MedadRufus/MastersProject/Bike_logger/references/cyclical power.PNG

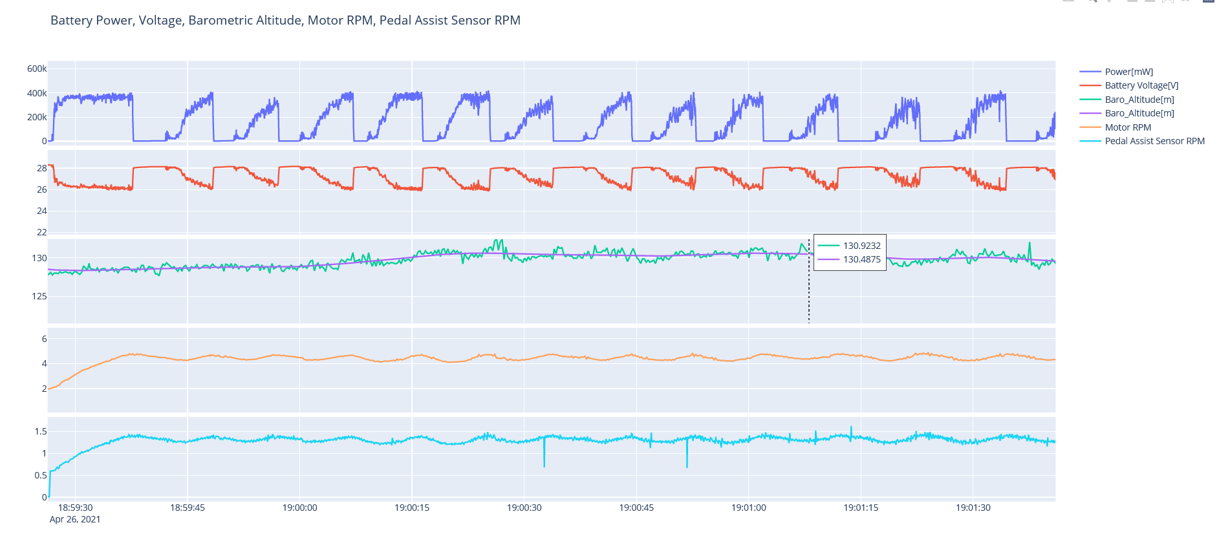
Bike_logger/references/cyclical power.PNG
