MedadRufus/MastersProject/Bike_logger/references/Discharge simulation.png

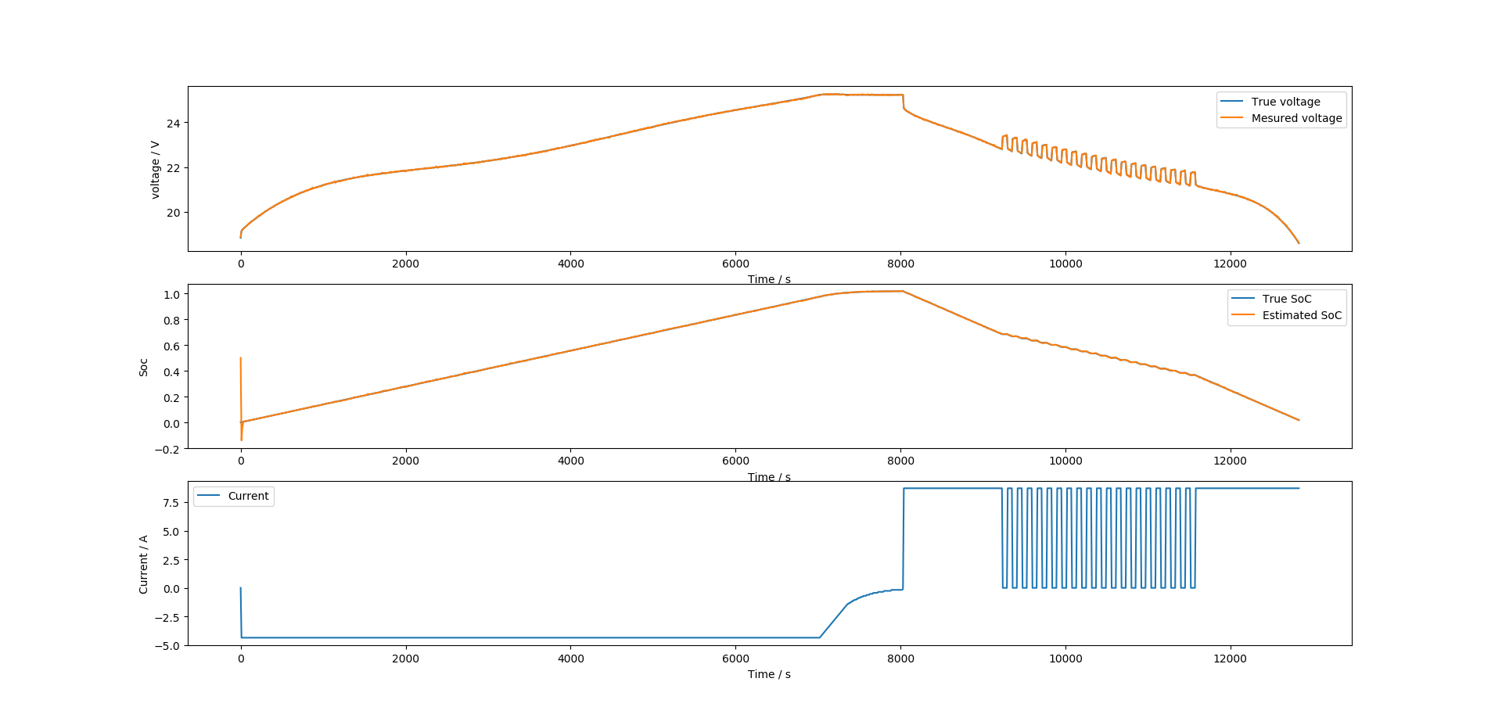
Bike_logger/references/Discharge simulation.png
