MedadRufus/MastersProject/Bike_logger/references/noise_on_brake_line.png

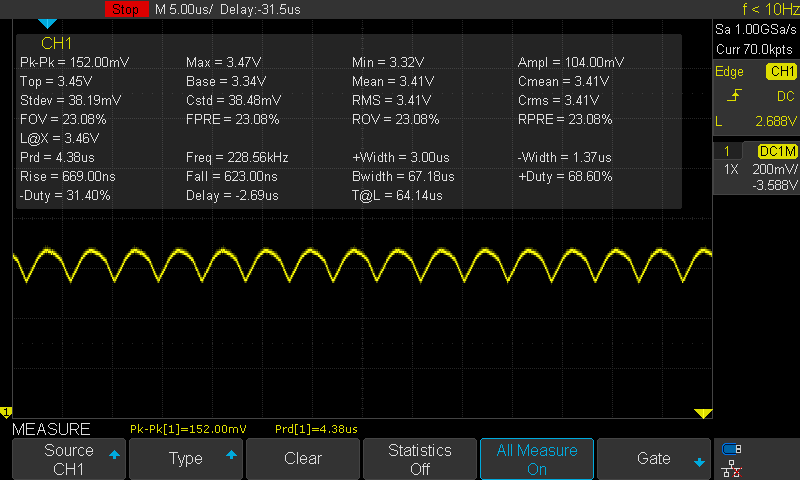
Bike_logger/references/noise_on_brake_line.png
