MedadRufus/MastersProject/Bike_logger/references/Plot prediction of power from slope.png

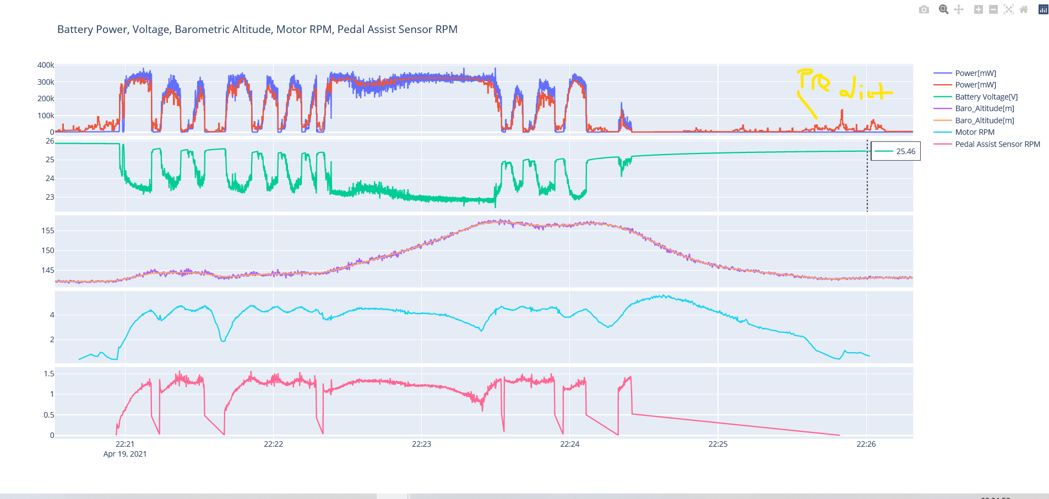
Bike_logger/references/Plot prediction of power from slope.png
