MedadRufus/MastersProject/Bike_logger/references/PNG/SDS00001.png

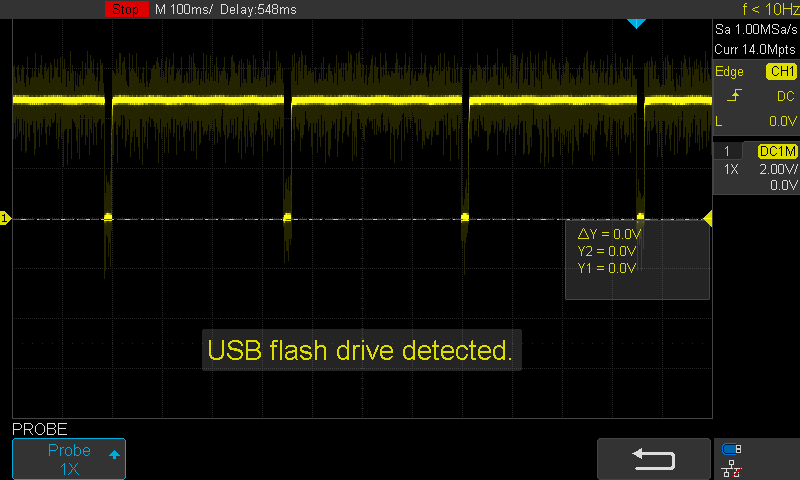
Bike_logger/references/PNG/SDS00001.png
