MedadRufus/MastersProject/Bike_logger/references/PNG/SDS00002.png

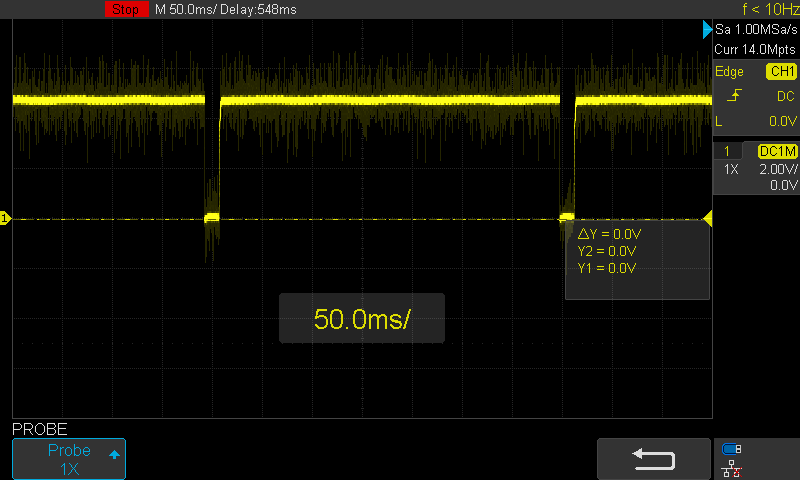
Bike_logger/references/PNG/SDS00002.png
