MedadRufus/MastersProject/Bike_logger/references/PNG/SDS00003.png

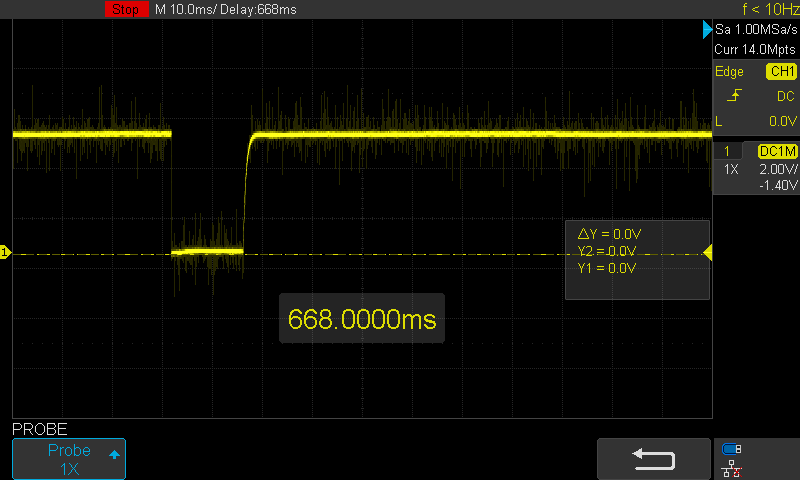
Bike_logger/references/PNG/SDS00003.png
