MedadRufus/MastersProject/Bike_logger/references/PNG/SDS00004.png

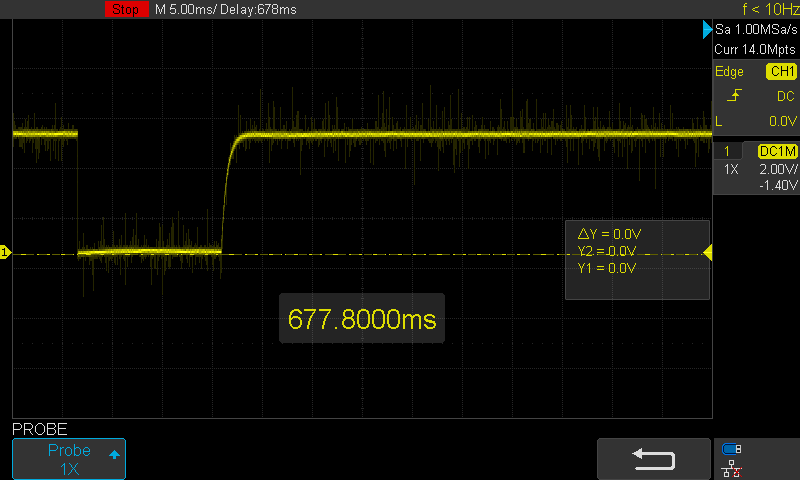
Bike_logger/references/PNG/SDS00004.png
