MedadRufus/MastersProject/Bike_logger/references/PNG/SDS00005.png

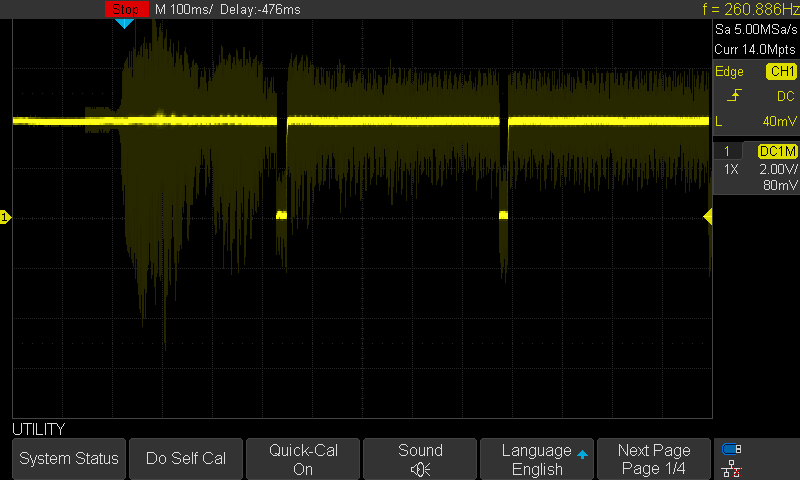
Bike_logger/references/PNG/SDS00005.png
