MedadRufus/MastersProject/Bike_logger/references/PNG/SDS00006.png

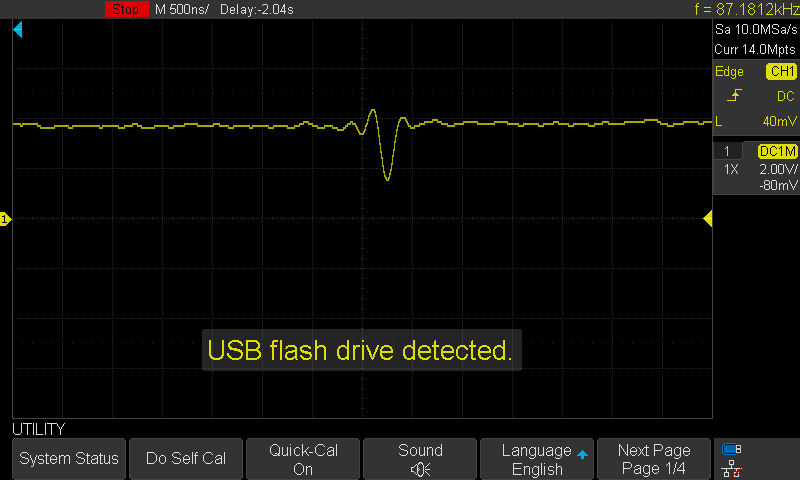
Bike_logger/references/PNG/SDS00006.png
