MedadRufus/MastersProject/Bike_logger/references/PNG/SDS00007.png

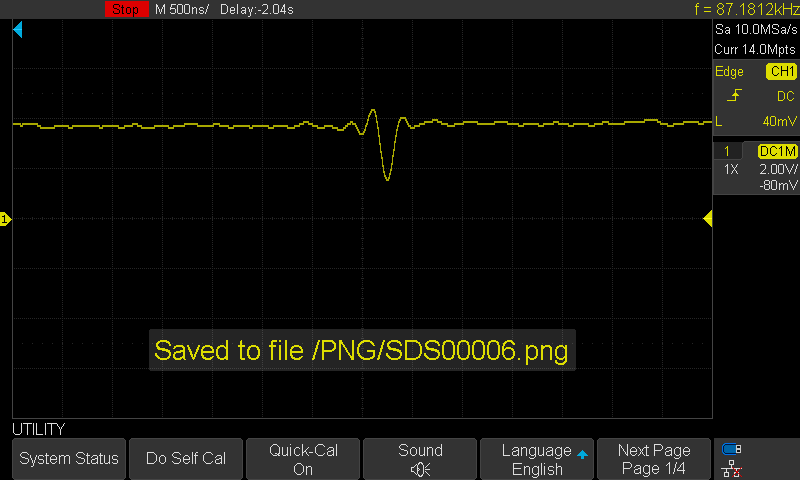
Bike_logger/references/PNG/SDS00007.png
