MedadRufus/MastersProject/Bike_logger/references/PNG/SDS00009.png

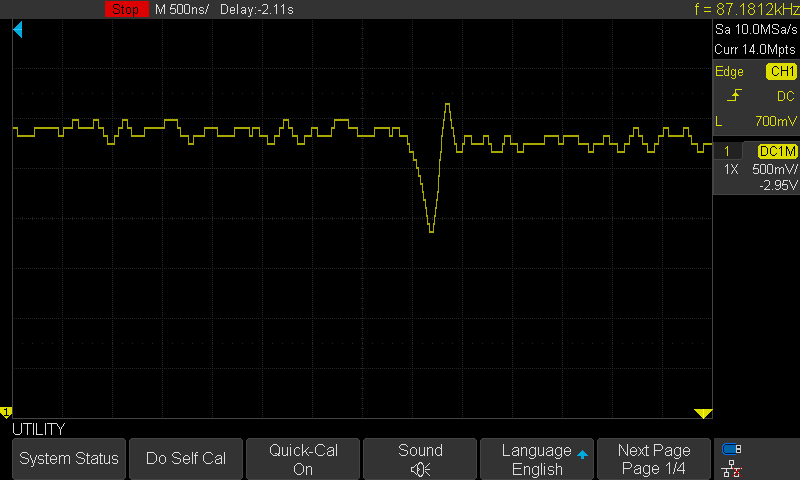
Bike_logger/references/PNG/SDS00009.png
