MedadRufus/MastersProject/Bike_logger/references/PNG/SDS00010.png

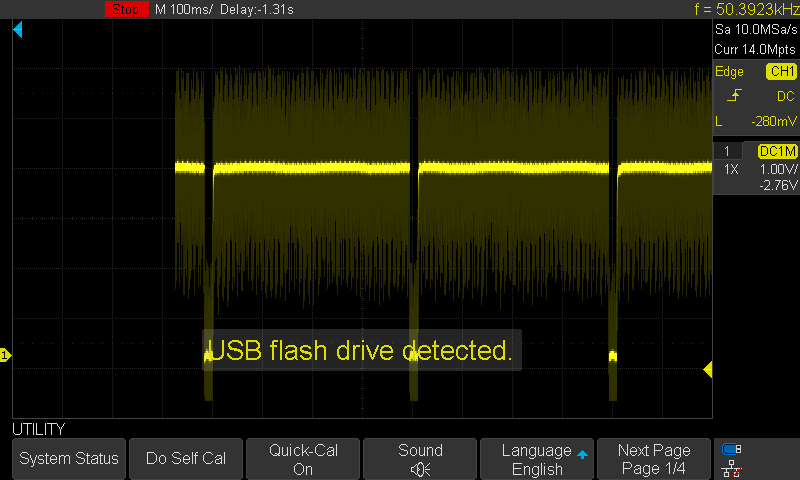
Bike_logger/references/PNG/SDS00010.png
