MedadRufus/MastersProject/Bike_logger/references/PNG/SDS00013.png

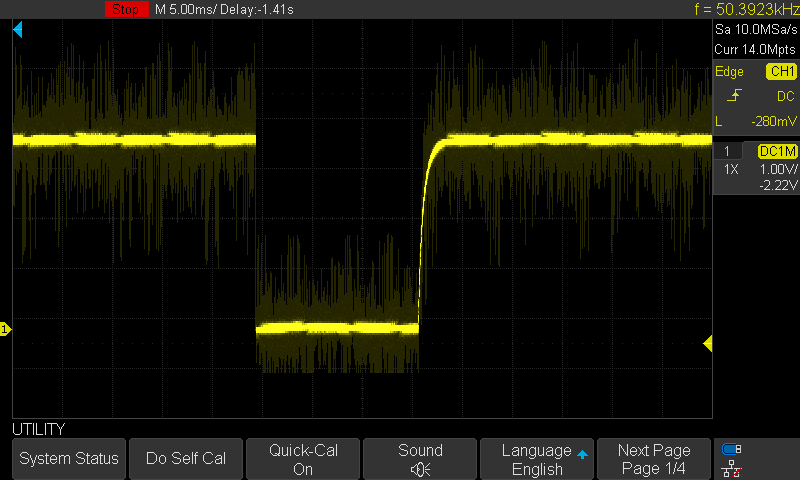
Bike_logger/references/PNG/SDS00013.png
