MedadRufus/MastersProject/Bike_logger/references/reference discharge plot.png

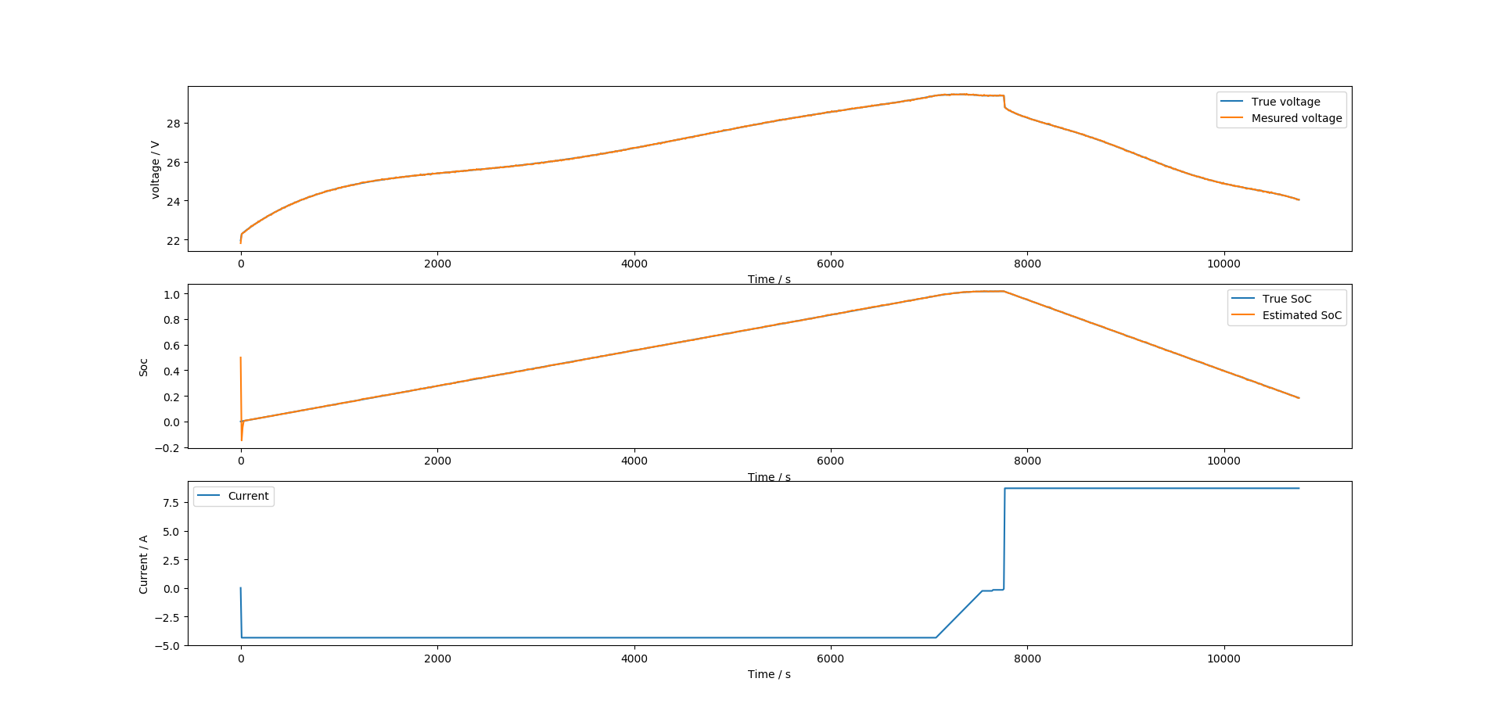
Bike_logger/references/reference discharge plot.png
