MedadRufus/MastersProject/Bike_logger/references/SDS00001.png

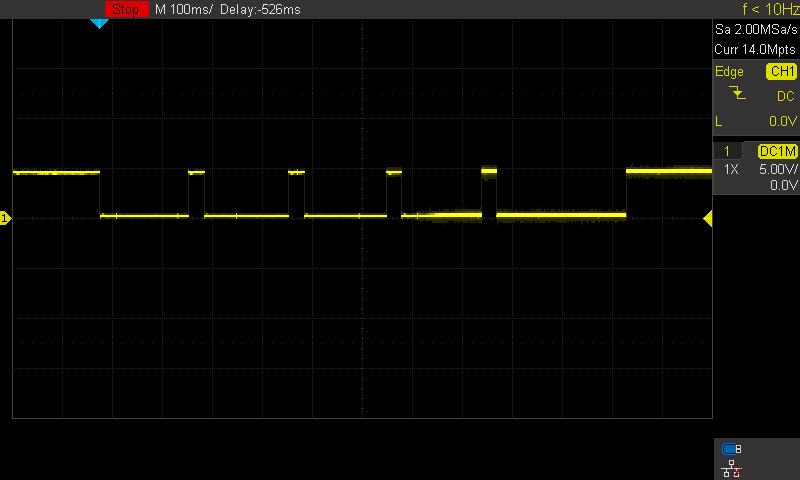
Bike_logger/references/SDS00001.png
