MedadRufus/MastersProject/Bike_logger/references/SDS00002.png

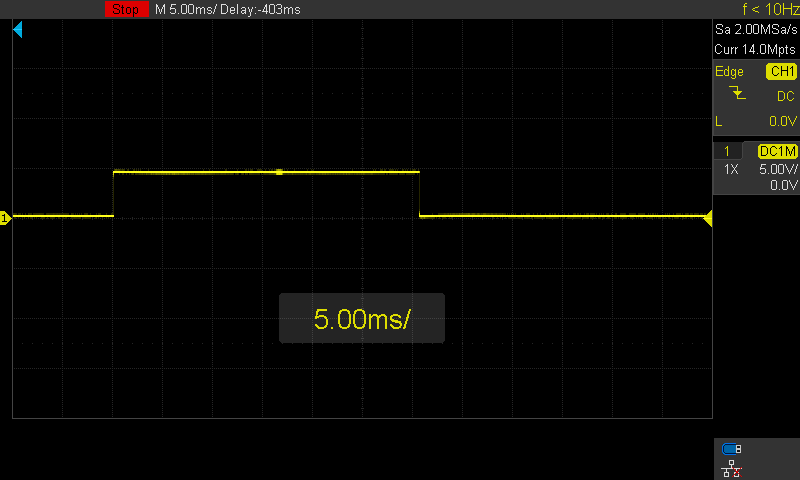
Bike_logger/references/SDS00002.png
