MedadRufus/MastersProject/Bike_logger/references/SDS00003.png

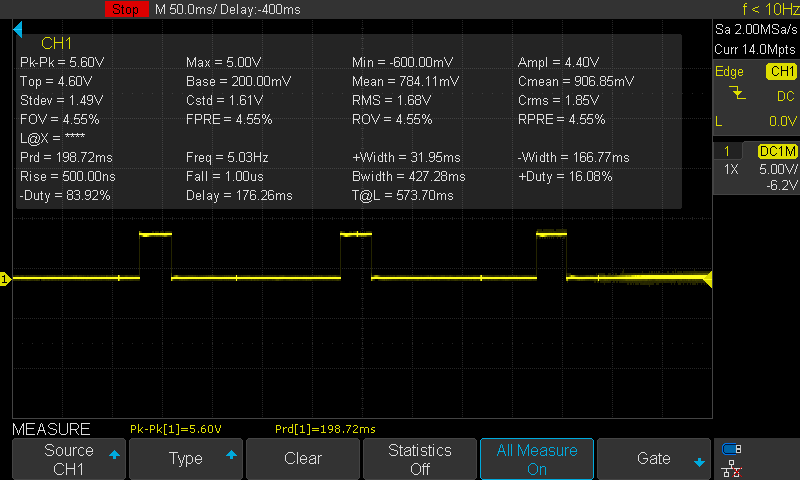
Bike_logger/references/SDS00003.png
