MedadRufus/MastersProject/Bike_logger/references/Low pass butterworth 4th order 10khz cutoff 10khz sample rate.png

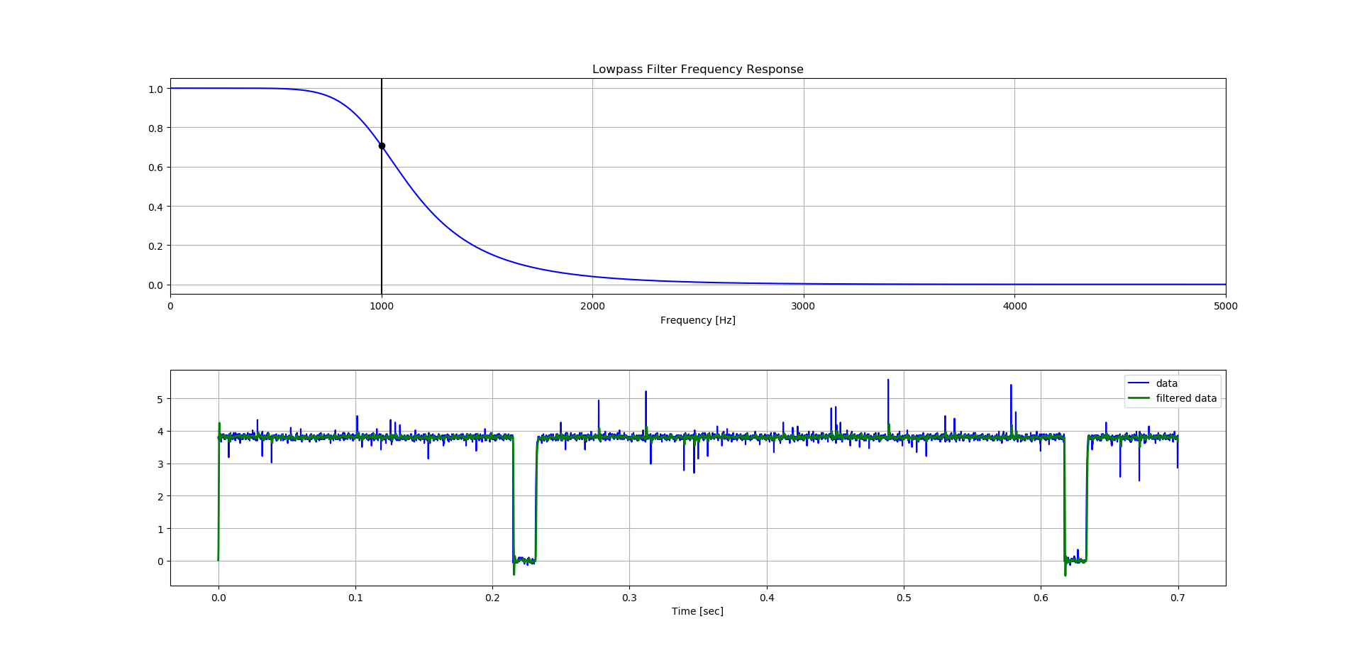
Bike_logger/references/Low pass butterworth 4th order 10khz cutoff 10khz sample rate.png
