MedadRufus/MastersProject/Bike_logger/references/Low pass butterworth 4th order 10000 cutoff.png

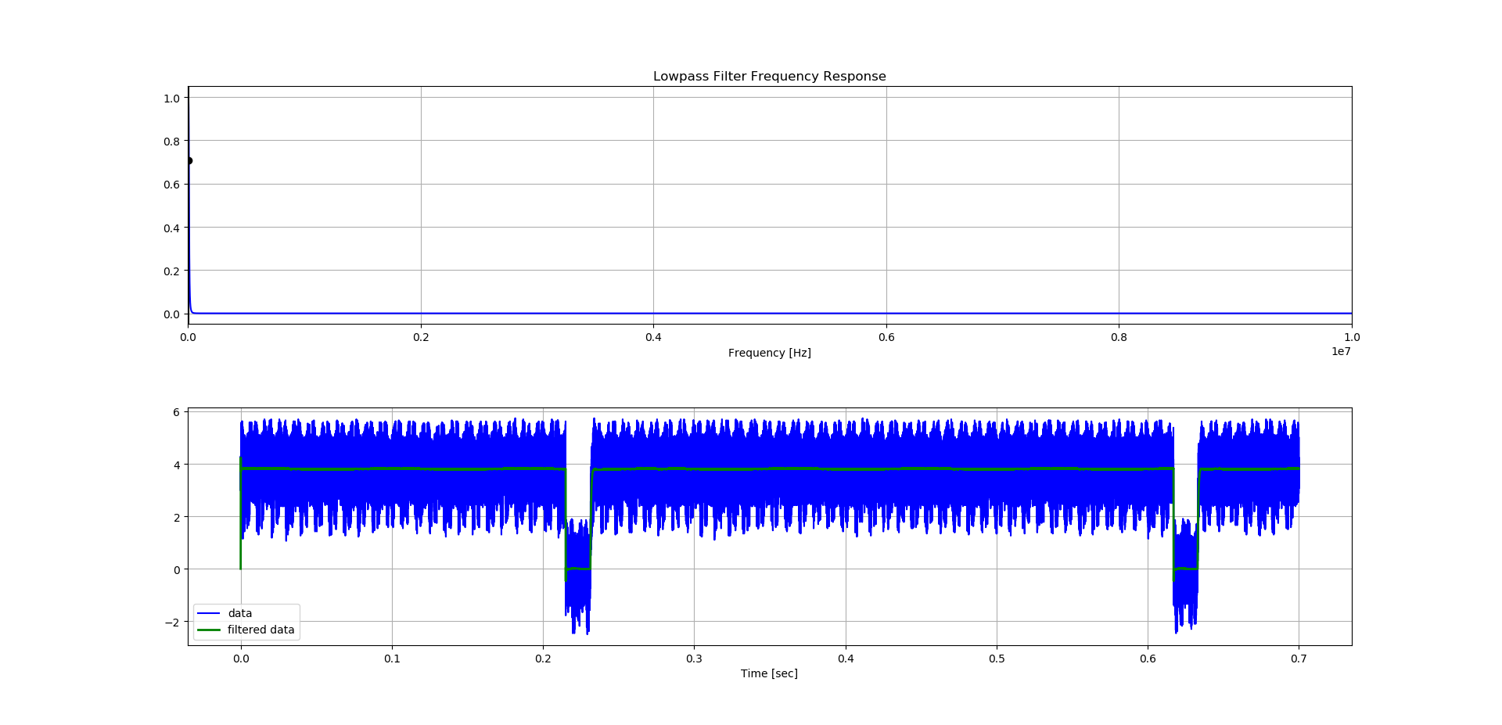
Bike_logger/references/Low pass butterworth 4th order 10000 cutoff.png
