MedadRufus/MastersProject/Bike_logger/references/Motor wiring.png

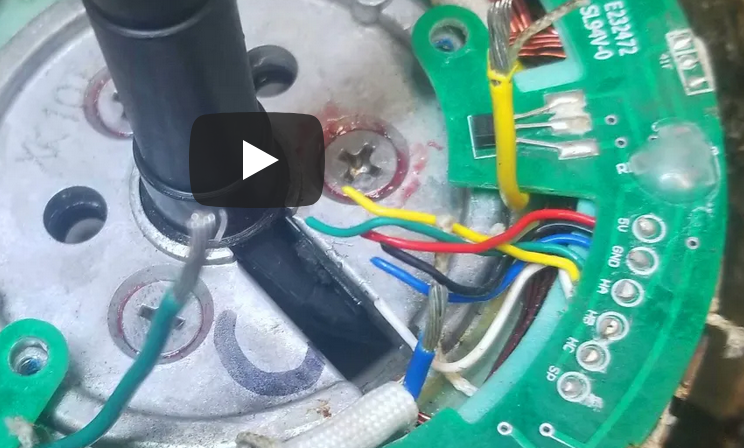
Bike_logger/references/Motor wiring.png
