MedadRufus/MastersProject/Bike_logger/Firmware/RTOS_sampling/src/state_logger/state_logger.hpp

/**
 * @file pulse_counter_adc.hpp
 * @author Medad Rufus Newman (mailto@medadnewman.co.uk)
 * @brief 
 * @version 0.1
 * @date 2021-04-19
 * 
 * @copyright Copyright (c) 2021
 * 
 */

void init_state_logger();
