MedadRufus/MastersProject/Bike_logger/Firmware/Firmware/Firmware.ino

/*********************************************************************
** @source Ebike Blackbox datalogger
**
** Main code for the Ebike logger
**
** @author Copyright (C) 2021  Medad Rufus Newman
** @version v0.1
********************************************************************/


/* ==================================================================== */
/* ========================== include files =========================== */
/* ==================================================================== */


/* Inclusion of system and local header files goes here */
#include <StateMachine.h>
#include "SparkFunLSM6DS3.h"
#include "Wire.h"
#include "SPI.h"
#include "ms8607.h"
#include "sd_card_manager.h"
#include <SparkFun_u-blox_GNSS_Arduino_Library.h> //http://librarymanager/All#SparkFun_u-blox_GNSS



/* ==================================================================== */
/* ============================ constants ============================= */
/* ==================================================================== */

/* #define and enum statements go here */

#define LED_PIN 27

#define RXD2 17
#define TXD2 16

/* ==================================================================== */
/* ======================== global variables ========================== */
/* ==================================================================== */

/* Global variables definitions go here */

StateMachine blinker1(100, true);
StateMachine poll_imu(1000, true);
StateMachine poll_baro(100, true);
StateMachine poll_gps(500, true);
StateMachine poll_IN226(10, true);
StateMachine write_to_sd(10, true);

const int led1 = LED_PIN;
bool state1 = false;   // false is OFF, true is ON

static ms8607 m_ms8607;
LSM6DS3 myIMU; //Default constructor is I2C, addr 0x6B
SD_Manager sd_manager;
SFE_UBLOX_GNSS myGNSS;

struct SensorData
{
  public:
    /* GPS related */
    uint32_t longitude;
    uint32_t latitude;
    uint32_t altitude;
    uint32_t velocity;
    uint32_t sats;

    /* Acceleration/Gyroscope */
    float acc_x;
    float acc_y;
    float acc_z;
    float gyro_x;
    float gyro_y;
    float gyro_z;
    float imu_temperature;

    /* Current voltage */
    int32_t current_discharge;
    int32_t voltage_discharge;
    int32_t current_charge;
    int32_t voltage_charge;

    /* Temperature/pressure/humidity */
    float temperature;
    float pressure;
    float humidity;

    /* Other physical inputs */
    int32_t pedal_rpm;
    bool brake_state;
    int32_t motor_speed;
};

SensorData sensor_data;

char buffer1 [50];
char buffer2 [200];
char buffer_gnss [400];


/* ==================================================================== */
/* ============================== data ================================ */
/* ==================================================================== */

/* Definition of datatypes go here */



/* ==================================================================== */
/* ==================== function prototypes =========================== */
/* ==================================================================== */

/* Function prototypes for public (external) functions go here */


/* ==================================================================== */
/* ============================ functions ============================= */
/* ==================================================================== */

void setup()
{
  pinMode(led1, OUTPUT);
  digitalWrite(led1, state1 ? HIGH : LOW);
  Wire.begin(21, 22); // Acclerometer/gyro/temperature/pressure/humidity sensor
  Wire.setClock(400000);

  Serial.begin(2000000);
  Serial.println("=======================================================");
  Serial.println("================ Ebike BlackBox =======================");
  Serial.println("============== By Medad Rufus Newman ==================");
  Serial.println("======= with assistance from Richard Ibbotson =========");
  Serial.println("=======================================================");

  /* Initialise the IMU */
  init_imu();


  m_ms8607.begin();
  if (m_ms8607.is_connected() == true) {
    m_ms8607.reset();
  }

  boolean connected = m_ms8607.is_connected();
  Serial.println(connected ? "MS8607 Sensor connencted" : "MS8607 Sensor disconnected");

  /* initiliase the SD card manager */
  sd_manager.SD_Manager_init();


  /* Setup GNSS */
  Serial1.begin(9600, SERIAL_8N1, RXD2, TXD2);
  //myGNSS.enableDebugging(); // Uncomment this line to enable helpful debug messages on Serial
  if (myGNSS.begin(Serial1) == false) //Connect to the u-blox module using Wire port
  {
    Serial.println(F("u-blox GNSS not detected"));
  }
  myGNSS.setI2COutput(COM_TYPE_UBX); //Set the I2C port to output UBX only (turn off NMEA noise)
  myGNSS.setNavigationFrequency(2); //Produce two solutions per second
  myGNSS.setAutoPVTcallback(&logPVTdata); // Enable automatic NAV PVT messages with callback to printPVTdata

}


void loop()
{
  if (blinker1.update()) {
    state1 = !state1;
    digitalWrite(led1, state1 ? HIGH : LOW);
  }

  if (poll_imu.update()) {
    //update_imu_data();
  }

  if (poll_baro.update()) {
    update_baro_data();
  }

  if (poll_gps.update()) {
    update_gnss_data();
  }

  if (poll_IN226.update()) {
  }

  if (write_to_sd.update()) {
  }
}

/* Update GNSS data */
void update_gnss_data()
{
  myGNSS.checkUblox(); // Check for the arrival of new data and process it.
  myGNSS.checkCallbacks(); // Check if any callbacks are waiting to be processed.
}

/* Update the sensor data struct with baro values

*/
void update_baro_data()
{
  //Get all parameters
  m_ms8607.read_temperature_pressure_humidity(&sensor_data.temperature, &sensor_data.pressure,
      &sensor_data.humidity);


  /* Write baro data to file */
  sprintf (buffer1, "%f,%f,%f\n", sensor_data.temperature, sensor_data.pressure, sensor_data.humidity);
  Serial.print(buffer1);
  sd_manager.appendFileSimple("/baro.csv", buffer1);

}


void init_imu()
{

  //Over-ride default settings if desired
  myIMU.settings.gyroEnabled = 1;  //Can be 0 or 1
  myIMU.settings.gyroRange = 2000;   //Max deg/s.  Can be: 125, 245, 500, 1000, 2000
  myIMU.settings.gyroSampleRate = 833;   //Hz.  Can be: 13, 26, 52, 104, 208, 416, 833, 1666
  myIMU.settings.gyroBandWidth = 200;  //Hz.  Can be: 50, 100, 200, 400;
  myIMU.settings.gyroFifoEnabled = 1;  //Set to include gyro in FIFO
  myIMU.settings.gyroFifoDecimation = 1;  //set 1 for on /1

  myIMU.settings.accelEnabled = 1;
  myIMU.settings.accelRange = 16;      //Max G force readable.  Can be: 2, 4, 8, 16
  myIMU.settings.accelSampleRate = 833;  //Hz.  Can be: 13, 26, 52, 104, 208, 416, 833, 1666, 3332, 6664, 13330
  myIMU.settings.accelBandWidth = 200;  //Hz.  Can be: 50, 100, 200, 400;
  myIMU.settings.accelFifoEnabled = 1;  //Set to include accelerometer in the FIFO
  myIMU.settings.accelFifoDecimation = 1;  //set 1 for on /1
  myIMU.settings.tempEnabled = 1;

  //Non-basic mode settings
  myIMU.settings.commMode = 1;

  //FIFO control settings
  myIMU.settings.fifoThreshold = 4095;  //Can be 0 to 4095 (16 bit bytes)
  myIMU.settings.fifoSampleRate = 100;  //Hz.  Can be: 10, 25, 50, 100, 200, 400, 800, 1600, 3300, 6600
  myIMU.settings.fifoModeWord = 6;  //FIFO mode.
  //FIFO mode.  Can be:
  //  0 (Bypass mode, FIFO off)
  //  1 (Stop when full)
  //  3 (Continuous during trigger)
  //  4 (Bypass until trigger)
  //  6 (Continous mode)

  //Call .begin() to configure the IMUs
  if ( myIMU.begin() != 0 )
  {
    Serial.println("Problem starting the IMU sensor");
  }
  else
  {
    Serial.println("Sensor IMU started.");
  }

  Serial.print("Configuring FIFO with no error checking...");
  myIMU.fifoBegin();
  Serial.print("Done!\n");

  Serial.print("Clearing out the FIFO...");
  myIMU.fifoClear();
  Serial.print("Done!\n");
}


/* Update the sensor data struct with imu values

*/
void update_imu_data()
{
  float temp;  //This is to hold read data

  //Now loop until FIFO is empty.  NOTE:  As the FIFO is only 8 bits wide,
  //the channels must be synchronized to a known position for the data to align
  //properly.  Emptying the fifo is one way of doing this (this example)
  while ( ( myIMU.fifoGetStatus() & 0x1000 ) == 0 ) {


    sprintf (buffer2, "%f,%f,%f,%f,%f,%f\n",
             myIMU.calcGyro(myIMU.fifoRead()),
             myIMU.calcGyro(myIMU.fifoRead()),
             myIMU.calcGyro(myIMU.fifoRead()),
             myIMU.calcAccel(myIMU.fifoRead()),
             myIMU.calcAccel(myIMU.fifoRead()),
             myIMU.calcAccel(myIMU.fifoRead())
            );

    Serial.print(buffer2);
    sd_manager.appendFileSimple("/imu.csv", buffer2);


  }

}


/*  Callback: printPVTdata will be called when new NAV PVT data arrives
    See u-blox_structs.h for the full definition of UBX_NAV_PVT_data_t
*/
void logPVTdata(UBX_NAV_PVT_data_t ubxDataStruct)
{

  sprintf (buffer_gnss,"%02u,%02u,%02u,%03u,%d,%d,%d,%d,%d,%d,%d\n",
          ubxDataStruct.hour,
          ubxDataStruct.min,
          ubxDataStruct.sec,
          ubxDataStruct.iTOW % 1000,
          ubxDataStruct.lat,
          ubxDataStruct.lon,
          ubxDataStruct.hMSL,
          ubxDataStruct.numSV,
          ubxDataStruct.gSpeed,
          ubxDataStruct.flags.bits.gnssFixOK,
          ubxDataStruct.fixType
         );

  Serial.print(buffer_gnss);
  sd_manager.appendFileSimple("/gnss.csv", buffer_gnss);
}
