MedadRufus/MastersProject/Bike_logger/Firmware/advancedExample_ntplib/advancedExample_ntplib.ino

#include <Arduino.h>

#include "WifiConfig.h"
#include <ESPNtpClient.h>
#ifdef ESP32
#include <WiFi.h>
#else
#include <ESP8266WiFi.h>
#endif

#ifndef WIFI_CONFIG_H
#define YOUR_WIFI_SSID "YOUR_WIFI_SSID"
#define YOUR_WIFI_PASSWD "YOUR_WIFI_PASSWD"
#endif // !WIFI_CONFIG_H

#ifdef ESP32
#define ONBOARDLED 5 // Built in LED on some ESP-32 boards
#else
#define ONBOARDLED 2 // Built in LED on ESP-12/ESP-07
#endif
#define SHOW_TIME_PERIOD 1000
#define NTP_TIMEOUT 1500

const PROGMEM char* ntpServer = "pool.ntp.org";
bool wifiFirstConnected = false;

boolean syncEventTriggered = false; // True if a time even has been triggered
NTPEvent_t ntpEvent; // Last triggered event
double offset;
double timedelay;

#ifdef ESP32
void onWifiEvent (system_event_id_t event, system_event_info_t info) {
#else
void onWifiEvent (WiFiEvent_t event) {
#endif
    Serial.printf ("[WiFi-event] event: %d\n", event);

    switch (event) {
#ifdef ESP32
    case SYSTEM_EVENT_STA_CONNECTED:
        Serial.printf ("Connected to %s. Asking for IP address.\r\n", info.connected.ssid);
        break;
    case SYSTEM_EVENT_STA_GOT_IP:
        Serial.printf ("Got IP: %s\r\n", IPAddress (info.got_ip.ip_info.ip.addr).toString ().c_str ());
        Serial.printf ("Connected: %s\r\n", WiFi.status () == WL_CONNECTED ? "yes" : "no");
        digitalWrite (ONBOARDLED, LOW); // Turn on LED
        wifiFirstConnected = true;
        break;
    case SYSTEM_EVENT_STA_DISCONNECTED:
        Serial.printf ("Disconnected from SSID: %s\n", info.disconnected.ssid);
        Serial.printf ("Reason: %d\n", info.disconnected.reason);
        digitalWrite (ONBOARDLED, HIGH); // Turn off LED
        //NTP.stop(); // NTP sync can be disabled to avoid sync errors
        WiFi.reconnect ();
        break;
#else
    case WIFI_EVENT_STAMODE_CONNECTED:
        Serial.printf ("Connected to %s. Asking for IP address.\r\n", WiFi.BSSIDstr().c_str());
        break;
    case WIFI_EVENT_STAMODE_GOT_IP:
        Serial.printf ("Got IP: %s\r\n", WiFi.localIP().toString().c_str ());
        Serial.printf ("Connected: %s\r\n", WiFi.status () == WL_CONNECTED ? "yes" : "no");
        digitalWrite (ONBOARDLED, LOW); // Turn on LED
        wifiFirstConnected = true;
        break;
    case WIFI_EVENT_STAMODE_DISCONNECTED:
        Serial.printf ("Disconnected from SSID: %s\n", WiFi.BSSIDstr ().c_str ());
        //Serial.printf ("Reason: %d\n", info.disconnected.reason);
        digitalWrite (ONBOARDLED, HIGH); // Turn off LED
        //NTP.stop(); // NTP sync can be disabled to avoid sync errors
        WiFi.reconnect ();
        break;
#endif
    default:
        break;
    }
}

void processSyncEvent (NTPEvent_t ntpEvent) {
    switch (ntpEvent.event) {
        case timeSyncd:
        case partlySync:
        case syncNotNeeded:
        case accuracyError:
            Serial.printf ("[NTP-event] %s\n", NTP.ntpEvent2str (ntpEvent));
            break;
        default:
            break;
    }
}

void setup() {
    Serial.begin (115200);
    Serial.println ();
    WiFi.mode (WIFI_STA);
    WiFi.begin (YOUR_WIFI_SSID, YOUR_WIFI_PASSWD);
    
    pinMode (ONBOARDLED, OUTPUT); // Onboard LED
    digitalWrite (ONBOARDLED, HIGH); // Switch off LED
    
    NTP.onNTPSyncEvent ([] (NTPEvent_t event) {
        ntpEvent = event;
        syncEventTriggered = true;
    });
    WiFi.onEvent (onWifiEvent);
}

void loop() {
    static int i = 0;
    static int last = 0;

    if (wifiFirstConnected) {
        wifiFirstConnected = false;
        NTP.setTimeZone (TZ_Europe_Madrid);
        NTP.setInterval (600);
        NTP.setNTPTimeout (NTP_TIMEOUT);
        // NTP.setMinSyncAccuracy (750);
        // NTP.settimeSyncThreshold (500);
        NTP.begin (ntpServer);
    }

    if (syncEventTriggered) {
        syncEventTriggered = false;
        processSyncEvent (ntpEvent);
    }

    if ((millis () - last) > SHOW_TIME_PERIOD) {
        last = millis ();
        Serial.print (i); Serial.print (" ");
        Serial.print (NTP.getTimeDateStringUs ()); Serial.print (" ");
        Serial.print ("WiFi is ");
        Serial.print (WiFi.isConnected () ? "connected" : "not connected"); Serial.print (". ");
        Serial.print ("Uptime: ");
        Serial.print (NTP.getUptimeString ()); Serial.print (" since ");
        Serial.println (NTP.getTimeDateString (NTP.getFirstSyncUs ()));
        Serial.printf ("Free heap: %u\n", ESP.getFreeHeap ());
        i++;
    }
    delay (0);
}
