MedadRufus/MastersProject/Bike_logger/Firmware/wifi_ntp_test/wifi_ntp_test.ino

#include <WiFi.h>
#include "time.h"

const char* ssid       = "BT-T5AFN7";
const char* password   = "xNHNav9QvrEVkd";

const char* ntpServer = "pool.ntp.org";
const long  gmtOffset_sec = 3600;
const int   daylightOffset_sec = 3600;

void printLocalTime()
{
  struct tm timeinfo;
  if (!getLocalTime(&timeinfo)) {
    Serial.println("Failed to obtain time");
    return;
  }

  /* e.g. 2021-02-28T00:38:30 */
  Serial.println(&timeinfo, "%FT%T");

}

void setup()
{
  Serial.begin(115200);

  //connect to WiFi
  Serial.printf("Connecting to %s ", ssid);
  WiFi.begin(ssid, password);
  while (WiFi.status() != WL_CONNECTED) {
    delay(500);
    Serial.print(".");
  }
  Serial.println(" CONNECTED");

  //init and get the time
  configTime(gmtOffset_sec, daylightOffset_sec, ntpServer);
  printLocalTime();

  //disconnect WiFi as it's no longer needed
  WiFi.disconnect(true);
  WiFi.mode(WIFI_OFF);
}

void loop()
{
  delay(1000);
  printLocalTime();
}
