MedadRufus/MastersProject/Bike_logger/Firmware/lsm6d_example/lsm6d_example.ino

/******************************************************************************
  MinimalistExample.ino

  Marshall Taylor @ SparkFun Electronics
  May 20, 2015
  https://github.com/sparkfun/LSM6DS3_Breakout
  https://github.com/sparkfun/SparkFun_LSM6DS3_Arduino_Library

  Description:
  Most basic example of use.

  Example using the LSM6DS3 with basic settings.  This sketch collects Gyro and
  Accelerometer data every second, then presents it on the serial monitor.

  Resources:
  Uses Wire.h for i2c operation
  Uses SPI.h for SPI operation
  Either can be omitted if not used

  Development environment specifics:
  Arduino IDE 1.6.4
  Teensy loader 1.23

  Hardware connections:
  Connect I2C SDA line to A4
  Connect I2C SCL line to A5
  Connect GND and 3.3v power to the IMU

  This code is released under the [MIT License](http://opensource.org/licenses/MIT).

  Please review the LICENSE.md file included with this example. If you have any questions
  or concerns with licensing, please contact techsupport@sparkfun.com.

  Distributed as-is; no warranty is given.
******************************************************************************/

#include "SparkFunLSM6DS3.h"
#include "Wire.h"
#include "SPI.h"

LSM6DS3 myIMU; //Default constructor is I2C, addr 0x6B

void setup() {
  // put your setup code here, to run once:
  Serial.begin(115200);
  delay(1000); //relax...
  Serial.println("Processor came out of reset.\n");
  Wire.begin(21,22);
  //Call .begin() to configure the IMU
  myIMU.begin();

}


void loop()
{

  
  Serial.print("x_gyro:");
  Serial.print(myIMU.readFloatGyroX(), 4);
  Serial.print(",");
  Serial.print("y_gyro:");
  Serial.print(myIMU.readFloatGyroY(), 4);
  Serial.print(",");
  Serial.print("z_gyro ");
  Serial.println(myIMU.readFloatGyroZ(), 4);


  Serial.print("x_acc:");
  Serial.print(myIMU.readFloatAccelX(), 4);
  Serial.print(",");
  Serial.print("y_acc:");
  Serial.print(myIMU.readFloatAccelY(), 4);
  Serial.print(",");
  Serial.print("z_acc:");
  Serial.println(myIMU.readFloatAccelZ(), 4);


  Serial.print("Degrees_C:");
  Serial.println(myIMU.readTempC(), 4);


  delay(100);
}
