MedadRufus/MastersProject/Bike_logger/Firmware/ms8607_TE_Example/ms8607_TE_Example.ino

#include "ms8607.h"
#include "Wire.h"

static ms8607 m_ms8607;


void setup() {
  Wire.begin(21,22);

  Serial.begin(115200);

  Serial.println("==== TE Connectivity ====");
  Serial.println("======== MS8607 =========");
  Serial.println("======== Measure ========");

  m_ms8607.begin();
  if (m_ms8607.is_connected() == true) {
    m_ms8607.reset(); 
  }
}

void loop() {
  float temperature;
  float pressure;
  float humidity;
  boolean connected;

  connected = m_ms8607.is_connected();
  if (connected == true) {
    Serial.println(connected ? "Sensor connencted" : "Sensor disconnected");
    m_ms8607.read_temperature_pressure_humidity(&temperature, &pressure,
                                                &humidity);

    Serial.print("Tempeature = ");
    Serial.print(temperature);
    Serial.print((char)176);
    Serial.println(" C");

    Serial.print("Pressure = ");
    Serial.print(pressure);
    Serial.println(" hPa");

    Serial.print("Humidity = ");
    Serial.print(humidity);
    Serial.println(" %RH");

    Serial.println("");
  } else {
    Serial.println(connected ? "Sensor connencted" : "Sensor disconnected");
  }
  delay(10);
}
